Slober3/BeeHive/STL/Bijenkast - Kast +Dak + Raster bodem + vlieggat Assembly-2 Kast +Dak + Raster bodem Assembly-1 Kast +Dak Assembly-2 Dakje Assembly-1 19 korte zijde dakje buitenkant 19mm dikte-3.STL

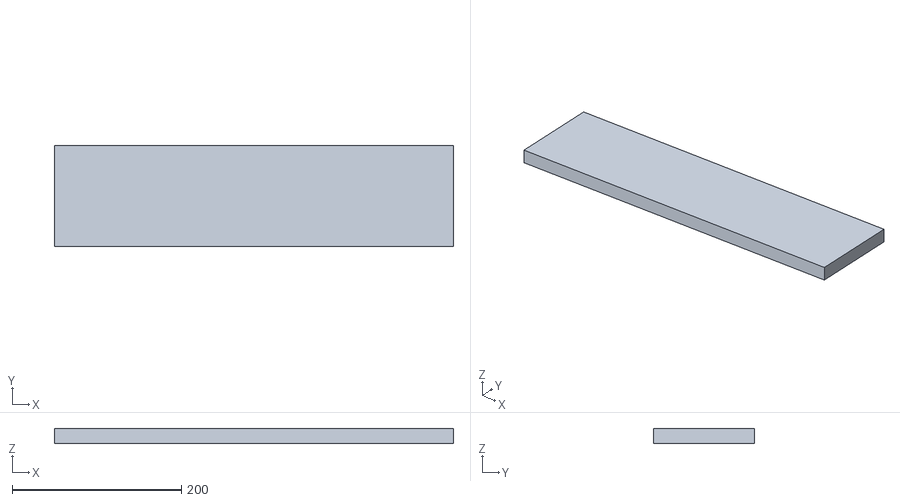
[picture p16: CAD file, 2019-03-04]
STL/Bijenkast - Kast +Dak + Raster bodem + vlieggat Assembly-2 Kast +Dak + Raster bodem Assembly-1 Kast +Dak Assembly-2 Dakje Assembly-1 19 korte zijde dakje buitenkant 19mm dikte-3.STL
472.0 x 120.0 x 18.0
