Slober3/BeeHive/STL/Bijenkast - Kast +Dak + Raster bodem + vlieggat Assembly-2 Kast +Dak + Raster bodem Assembly-1 Kast +Dak Assembly-2 Dakje Assembly-1 19 korte zijde dakje binnenkant 19mm dikte-2.STL

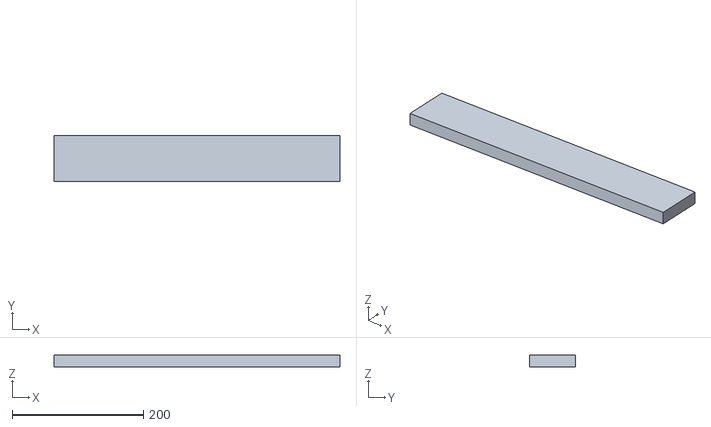
[picture p17: CAD file, 2019-03-04]
STL/Bijenkast - Kast +Dak + Raster bodem + vlieggat Assembly-2 Kast +Dak + Raster bodem Assembly-1 Kast +Dak Assembly-2 Dakje Assembly-1 19 korte zijde dakje binnenkant 19mm dikte-2.STL
436.0 x 70.0 x 18.0
