Slober3/BeeHive/STL/Bijenkast - Kast +Dak + Raster bodem + vlieggat Assembly-2 Kast +Dak + Raster bodem Assembly-1 Kast +Dak Assembly-2 Dakje Assembly-1 19 Bovenplaat van het deksel 19mm dikte-1.STL

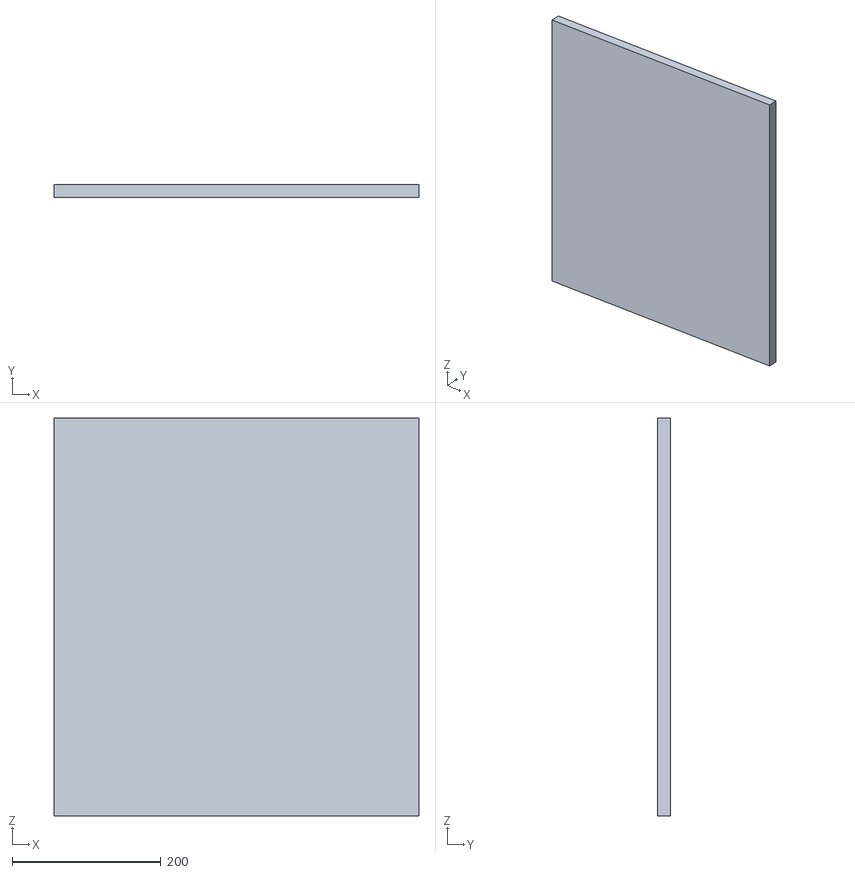
[picture p18: CAD file, 2019-03-04]
STL/Bijenkast - Kast +Dak + Raster bodem + vlieggat Assembly-2 Kast +Dak + Raster bodem Assembly-1 Kast +Dak Assembly-2 Dakje Assembly-1 19 Bovenplaat van het deksel 19mm dikte-1.STL
490.0 x 18.0 x 535.0
