Slober3/BeeHive/STL/Bijenkast - Kast +Dak + Raster bodem + vlieggat Assembly-2 Kast +Dak + Raster bodem Assembly-1 Kast +Dak Assembly-2 Kast Assembly-2 12 balkjes 12mm dikte-6.STL

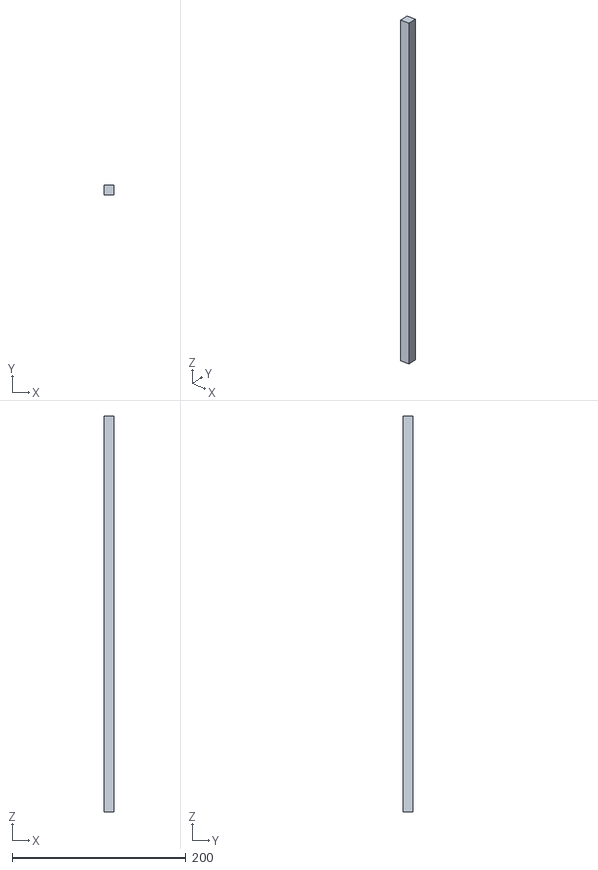
[picture p19: CAD file, 2019-03-04]
STL/Bijenkast - Kast +Dak + Raster bodem + vlieggat Assembly-2 Kast +Dak + Raster bodem Assembly-1 Kast +Dak Assembly-2 Kast Assembly-2 12 balkjes 12mm dikte-6.STL
12.0 x 12.0 x 456.0
