Slober3/BeeHive/STL/Bijenkast - Kast +Dak + Raster bodem + vlieggat Assembly-2 12 binnevlieggat 12mm dikte-1.STL

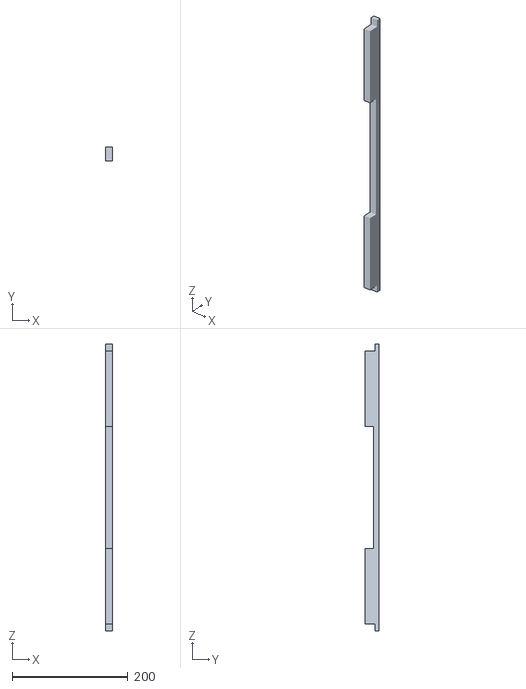
[picture p20: CAD file, 2019-03-04]
STL/Bijenkast - Kast +Dak + Raster bodem + vlieggat Assembly-2 12 binnevlieggat 12mm dikte-1.STL
12.0 x 25.0 x 495.0
