Slober3/BeeHive/SolidWorks/Solidwork parts/12 balkjes 12mm dikte.SLDPRT

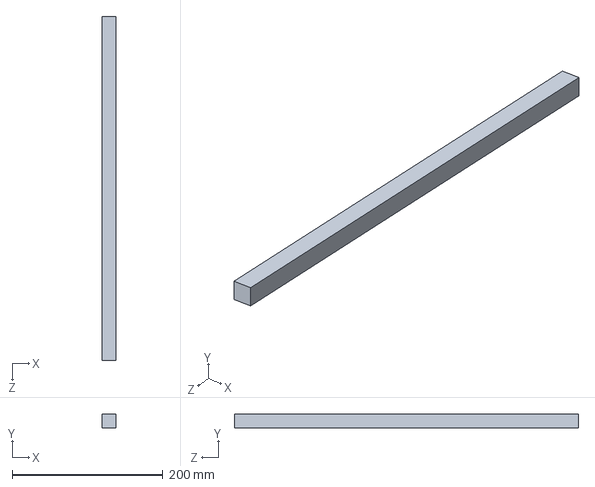
[picture p22: CAD file, 2019-03-18]
SolidWorks/Solidwork parts/12 balkjes 12mm dikte.SLDPRT
18.0 x 18.0 x 456.0 mm
