Slober3/BeeHive/SolidWorks/Solidwork parts/12 binnevlieggat 12mm dikte.SLDPRT

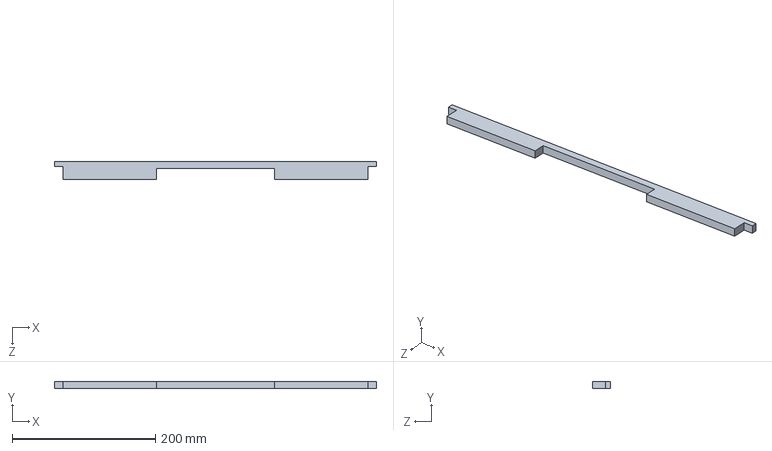
[picture p23: CAD file, 2019-03-04]
SolidWorks/Solidwork parts/12 binnevlieggat 12mm dikte.SLDPRT
450.0 x 10.0 x 25.0 mm
