Slober3/BeeHive/SolidWorks/Solidwork parts/Bodemplaat met opening voor raster 18mm.SLDPRT

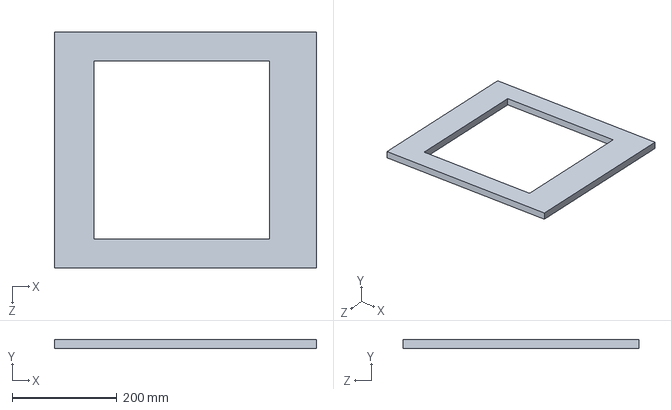
[picture p24: CAD file, 2019-03-04]
SolidWorks/Solidwork parts/Bodemplaat met opening voor raster 18mm.SLDPRT
500.0 x 18.0 x 450.0 mm
