Slober3/BeeHive/SolidWorks/Solidwork parts/Balkje kort voor verhoging bodemplaat met raster.SLDPRT

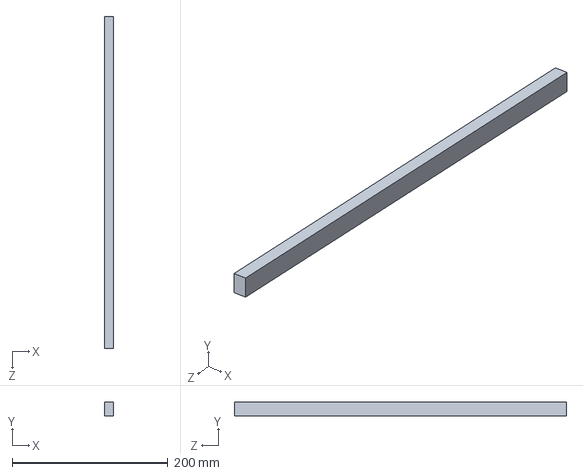
[picture p25: CAD file, 2019-03-04]
SolidWorks/Solidwork parts/Balkje kort voor verhoging bodemplaat met raster.SLDPRT
12.0 x 18.0 x 426.0 mm
