Slober3/BeeHive/SolidWorks/Solidwork parts/stopplankjes poten.SLDPRT

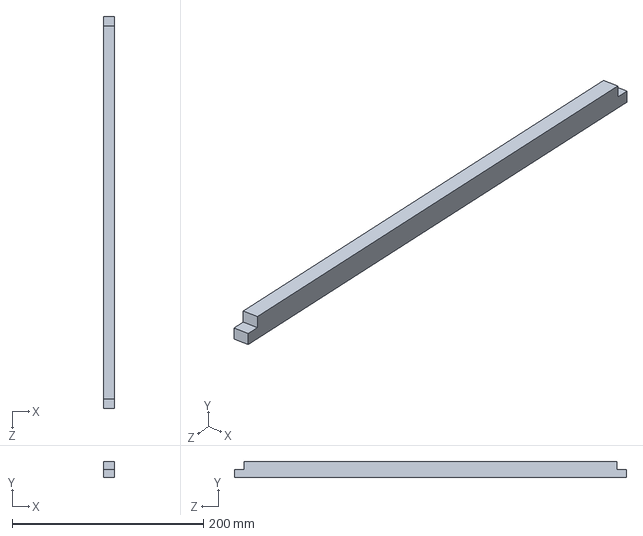
[picture p26: CAD file, 2019-03-04]
SolidWorks/Solidwork parts/stopplankjes poten.SLDPRT
12.0 x 17.0 x 410.0 mm
