Slober3/BeeHive/STL/Bijenkast - 30 voetstuk bijenkast bijenkasthouder links rechts 30mm dikte-2.STL

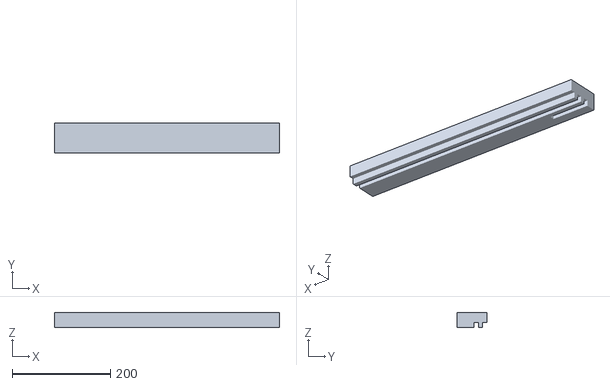
[picture p27: CAD file, 2019-03-04]
STL/Bijenkast - 30 voetstuk bijenkast bijenkasthouder links rechts 30mm dikte-2.STL
457.0 x 60.0 x 30.0
