Slober3/BeeHive/SolidWorks/Solidwork parts/luchtplaat afdichting bodem.SLDPRT

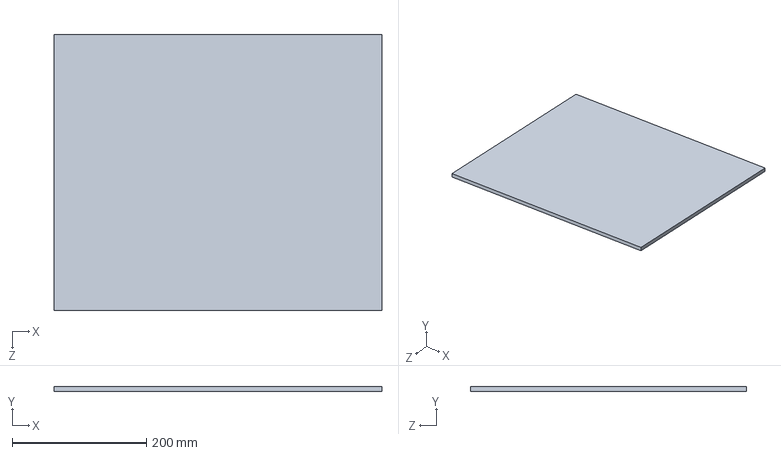
[picture p28: CAD file, 2019-03-04]
SolidWorks/Solidwork parts/luchtplaat afdichting bodem.SLDPRT
488.0 x 8.00 x 410.0 mm
