Slober3/BeeHive/SolidWorks/Solidwork parts/30 voetstuk bijenkast bijenkasthouder links rechts 30mm dikte.SLDPRT

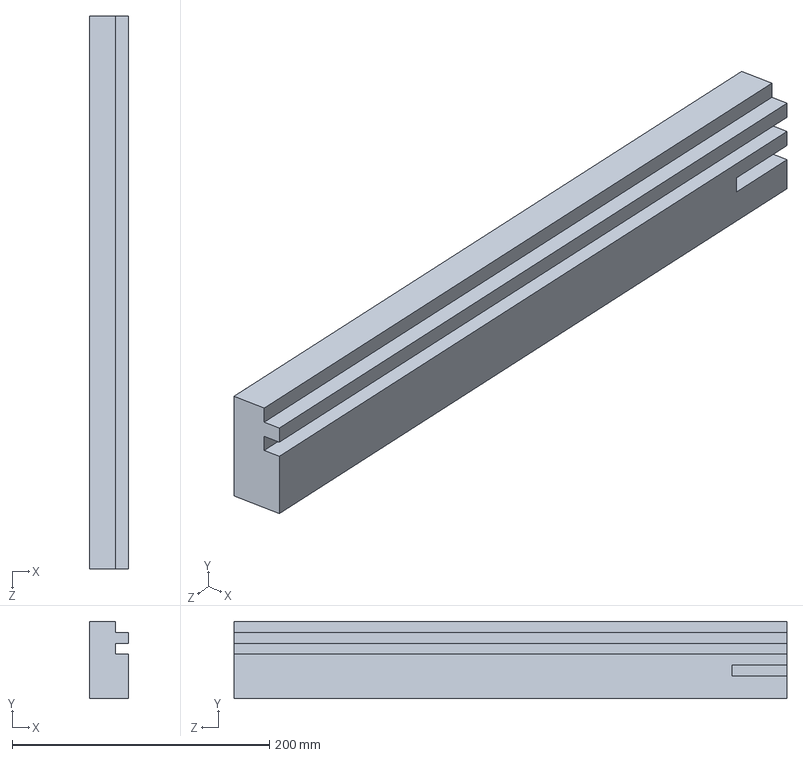
[picture p29: CAD file, 2019-03-04]
SolidWorks/Solidwork parts/30 voetstuk bijenkast bijenkasthouder links rechts 30mm dikte.SLDPRT
30.0 x 60.0 x 430.0 mm
