Slober3/BeeHive/SolidWorks/Solidwork parts/19 korte zijde dakje binnenkant 19mm dikte.SLDPRT

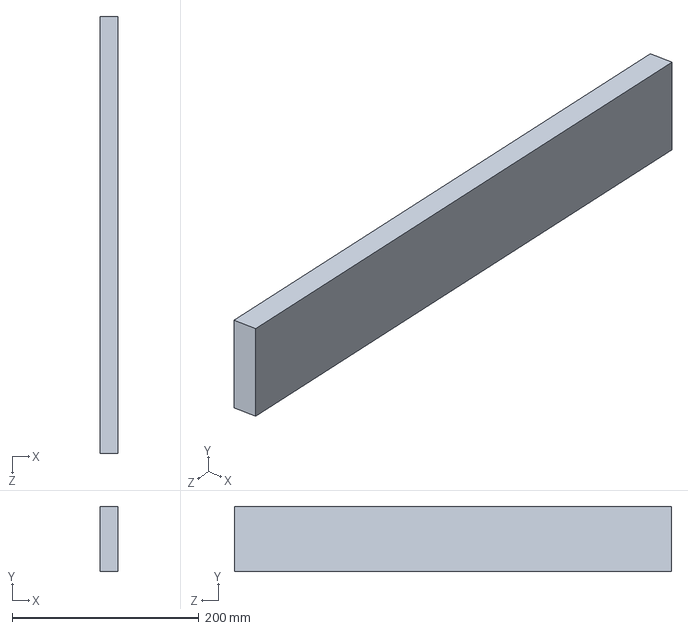
[picture p30: CAD file, 2019-03-04]
SolidWorks/Solidwork parts/19 korte zijde dakje binnenkant 19mm dikte.SLDPRT
19.0 x 70.0 x 468.0 mm
