Slober3/BeeHive/SolidWorks/Solidwork parts/19 korte zijde dakje buitenkant 19mm dikte.SLDPRT

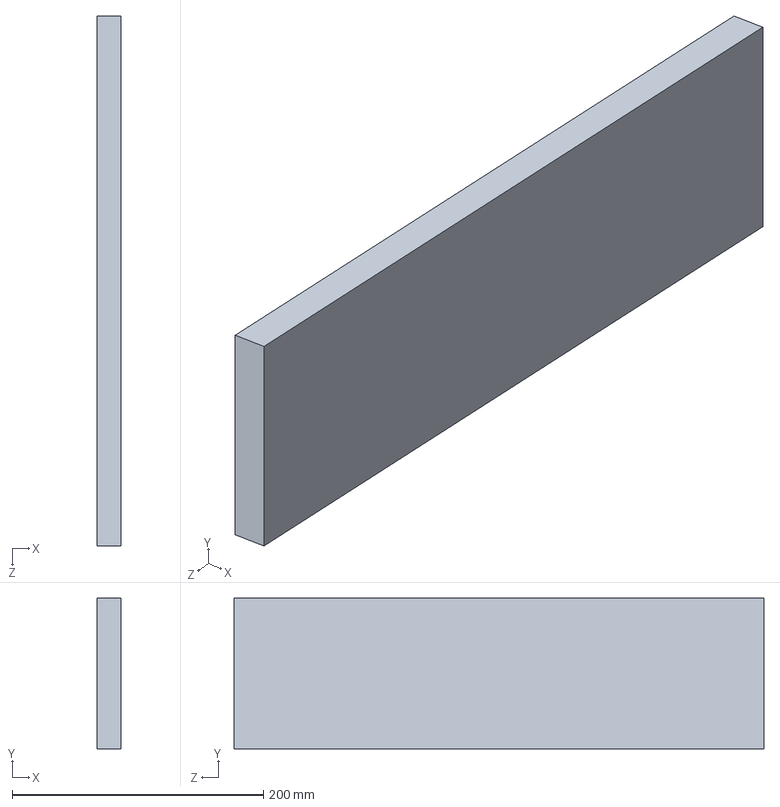
[picture p31: CAD file, 2019-03-04]
SolidWorks/Solidwork parts/19 korte zijde dakje buitenkant 19mm dikte.SLDPRT
19.0 x 120.0 x 422.0 mm
