Slober3/BeeHive/SolidWorks/Solidwork parts/19 lange buitenzijde 19mm dikte.SLDPRT

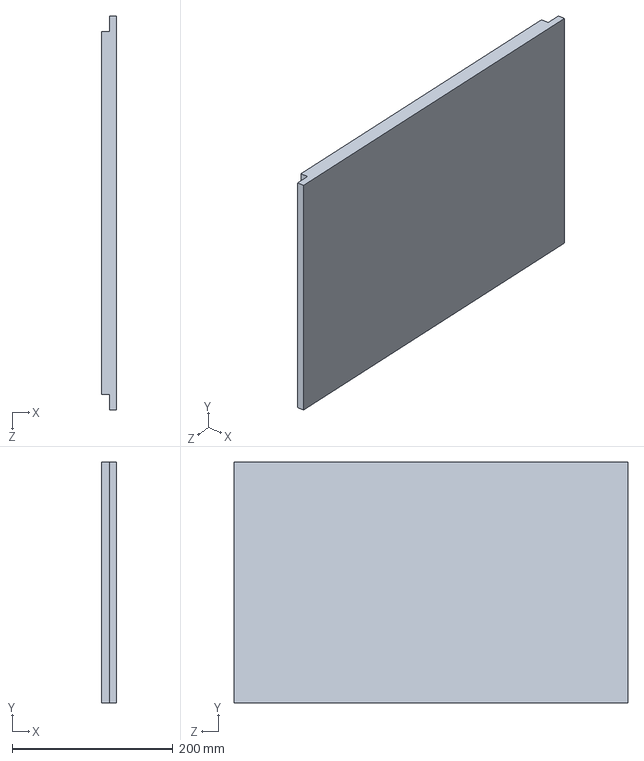
[picture p32: CAD file, 2019-03-04]
SolidWorks/Solidwork parts/19 lange buitenzijde 19mm dikte.SLDPRT
19.0 x 300.0 x 490.0 mm
