Slober3/BeeHive/SolidWorks/Solidwork parts/19 Korte buitenzijde 19mm dikte.SLDPRT

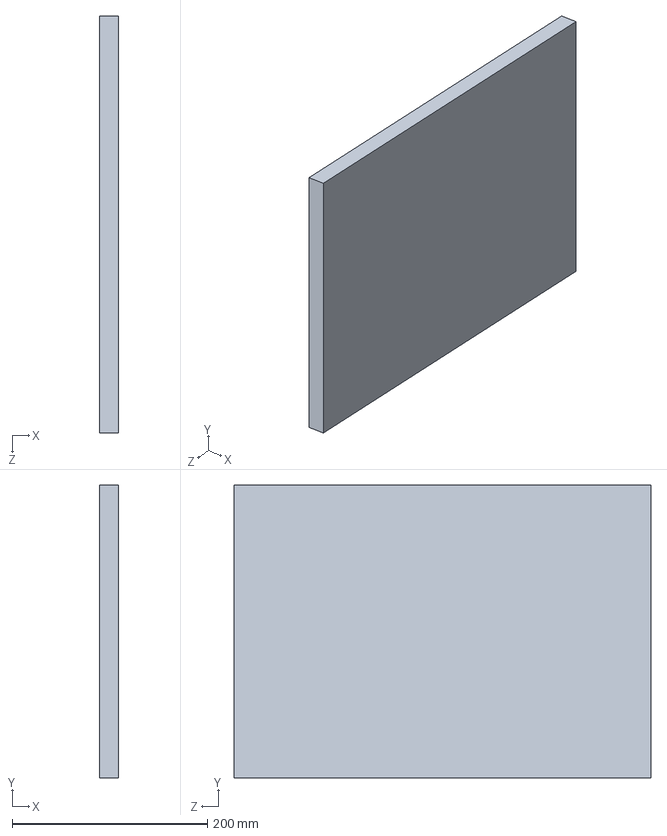
[picture p33: CAD file, 2019-03-04]
SolidWorks/Solidwork parts/19 Korte buitenzijde 19mm dikte.SLDPRT
19.0 x 300.0 x 427.0 mm
