Slober3/BeeHive/STL/Bijenkast - stopplankjes poten-8.STL

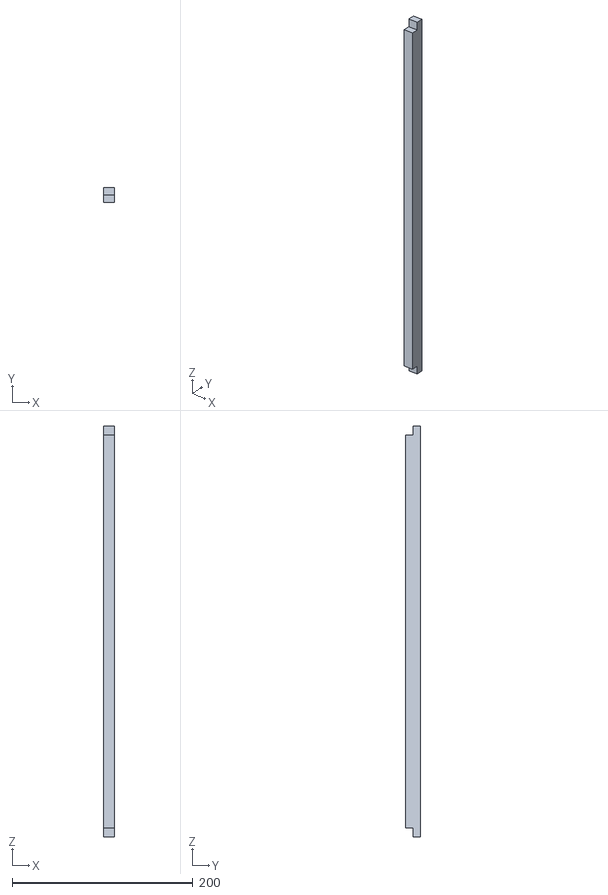
[picture p34: CAD file, 2019-03-04]
STL/Bijenkast - stopplankjes poten-8.STL
12.0 x 17.0 x 455.0
