Slober3/BeeHive/SolidWorks/Solidwork parts/19 Bovenplaat van het deksel 19mm dikte.SLDPRT

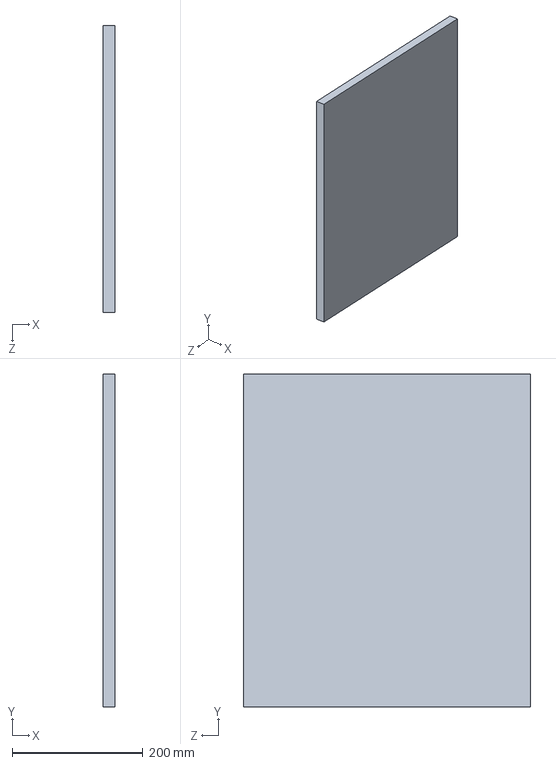
[picture p35: CAD file, 2019-03-04]
SolidWorks/Solidwork parts/19 Bovenplaat van het deksel 19mm dikte.SLDPRT
19.0 x 510.0 x 440.0 mm
