Slober3/BeeHive/SolidWorks/Solidwork parts/19 langste zijde dakje buitenkant 19mm dikte.SLDPRT

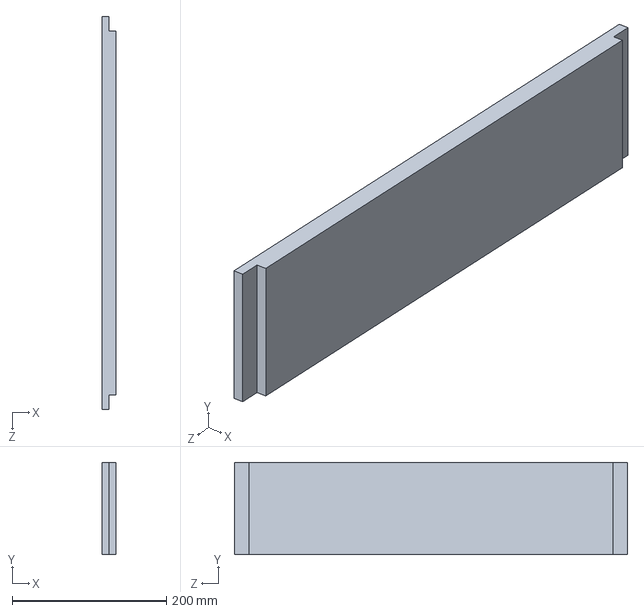
[picture p36: CAD file, 2019-03-03]
SolidWorks/Solidwork parts/19 langste zijde dakje buitenkant 19mm dikte.SLDPRT
18.0 x 120.0 x 510.0 mm
