Slober3/BeeHive/SolidWorks/Solidwork parts/19 langste zijde dakje binnenkant 19mm dikte.SLDPRT

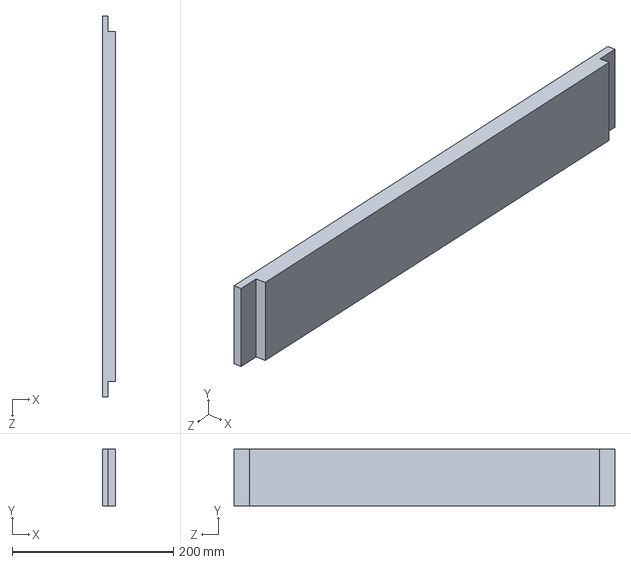
[picture p37: CAD file, 2019-03-03]
SolidWorks/Solidwork parts/19 langste zijde dakje binnenkant 19mm dikte.SLDPRT
16.0 x 70.0 x 472.0 mm
