Slober3/BeeHive/SolidWorks/Solidwork parts/Bovenplaat met gat (plexi).SLDPRT

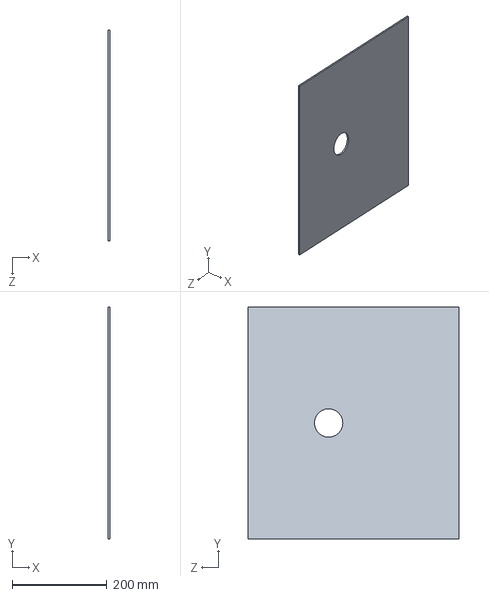
[picture p38: CAD file, 2019-02-09]
SolidWorks/Solidwork parts/Bovenplaat met gat (plexi).SLDPRT
4.00 x 490.0 x 445.0 mm
