Slober3/BeeHive/STL/Bijenkast - luchtplaat afdichting bodem-2.STL

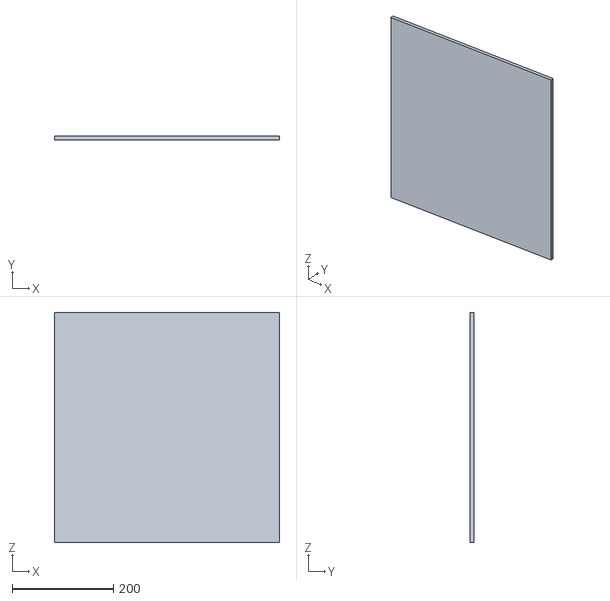
[picture p39: CAD file, 2019-03-04]
STL/Bijenkast - luchtplaat afdichting bodem-2.STL
445.0 x 8.00 x 455.0
